tin-box/Creten-Speaker/V4_OuterShell_R.stl

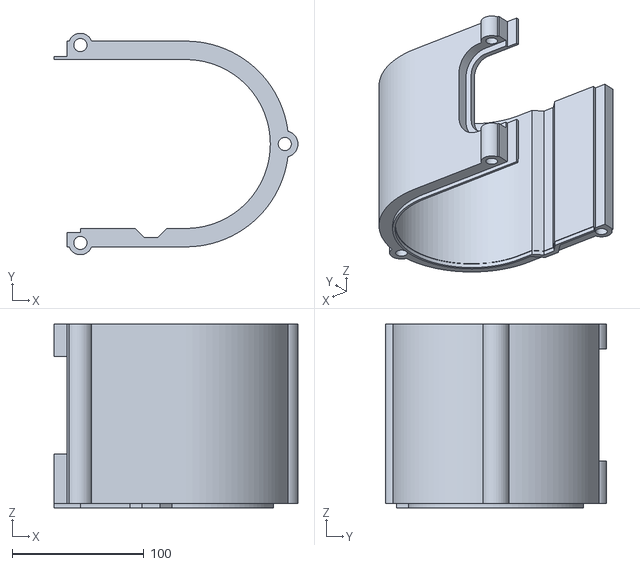
[picture p17: CAD file, 2023-01-02]
V4_OuterShell_R.stl
185.0 x 167.9 x 139.5
