tin-box/Creten-Speaker/V4_BottomPlate_L.stl

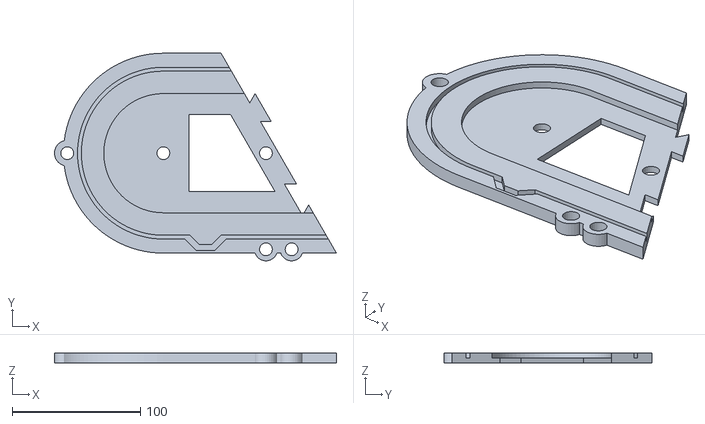
[picture p18: CAD file, 2023-01-02]
V4_BottomPlate_L.stl
220.0 x 162.0 x 8.00
