tin-box/Creten-Speaker/Long_Dual_Pin.stl

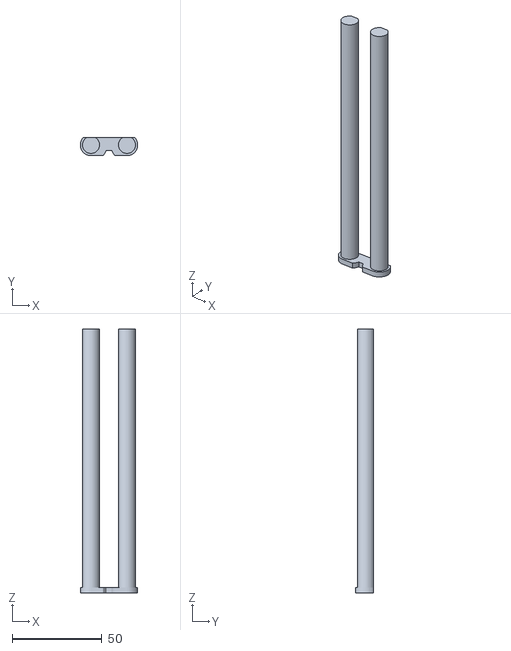
[picture p19: CAD file, 2023-01-02]
Long_Dual_Pin.stl
32.0 x 10.2 x 147.0
