tin-box/Creten-Speaker/QuadTopCap.stl

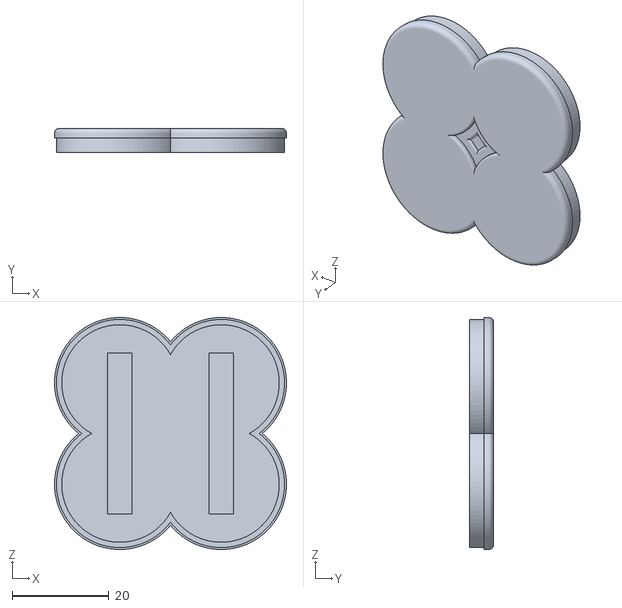
[picture p20: CAD file, 2023-01-02]
QuadTopCap.stl
48.0 x 5.00 x 48.0
