tin-box/Creten-Speaker/QuadControlPanelNoLamp.stl

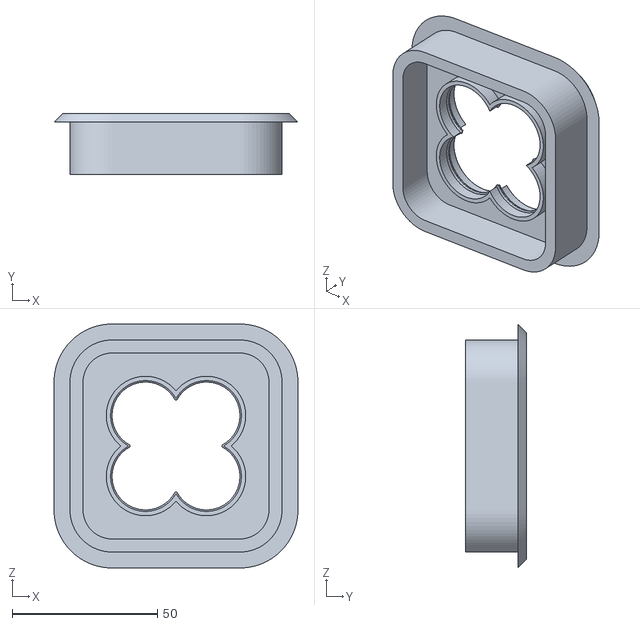
[picture p21: CAD file, 2023-01-02]
QuadControlPanelNoLamp.stl
84.0 x 21.0 x 84.0
