tin-box/Creten-Speaker/V4_PwrPlug.stl

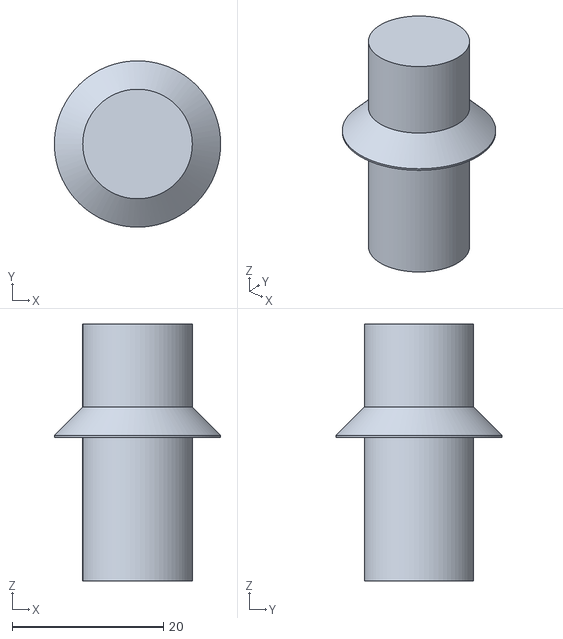
[picture p22: CAD file, 2023-01-02]
V4_PwrPlug.stl
22.0 x 22.0 x 34.0
