tin-box/Creten-Speaker/V4_VolKnob6mm.stl

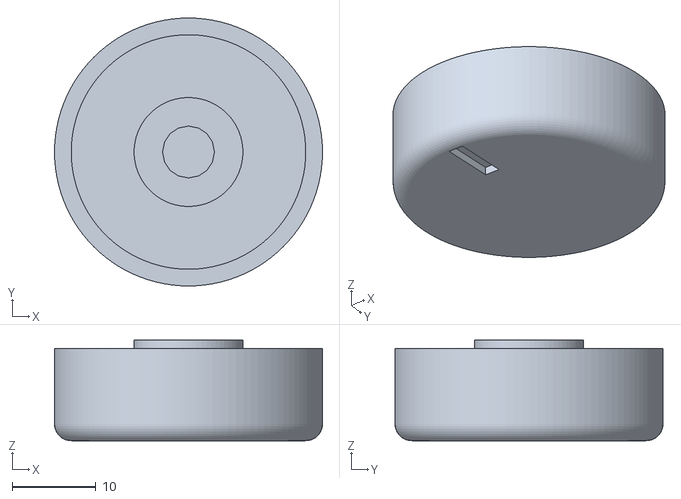
[picture p23: CAD file, 2023-01-02]
V4_VolKnob6mm.stl
32.0 x 32.0 x 12.0
