tin-box/Creten-Speaker/Quad18650Tube.stl

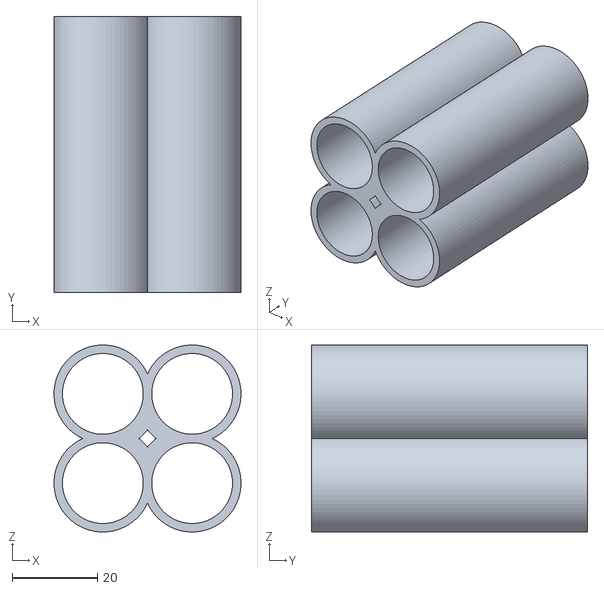
[picture p24: CAD file, 2023-01-02]
Quad18650Tube.stl
44.0 x 65.0 x 44.0
