tin-box/Creten-Speaker/V4Nut.stl

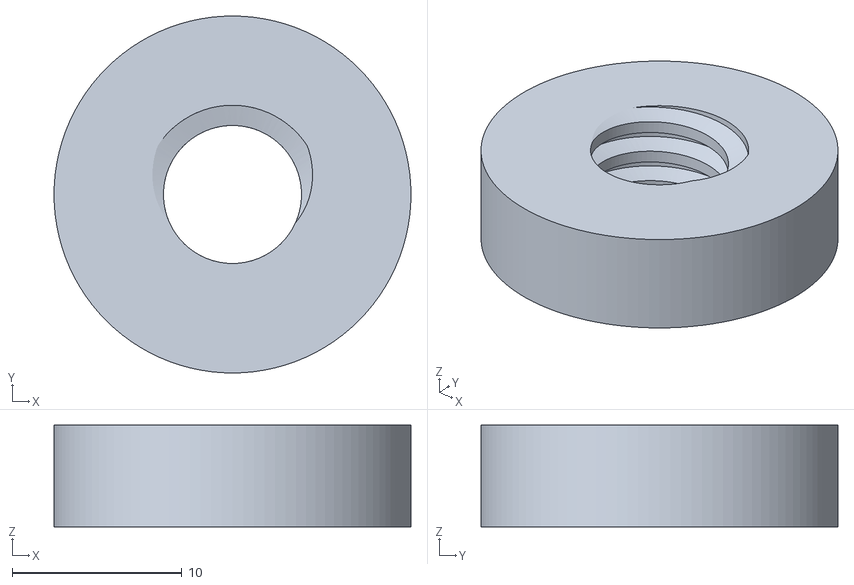
[picture p25: CAD file, 2023-01-02]
V4Nut.stl
21.0 x 21.0 x 6.00
