tin-box/Creten-Speaker/V4_QuadControlPanel_V3.stl

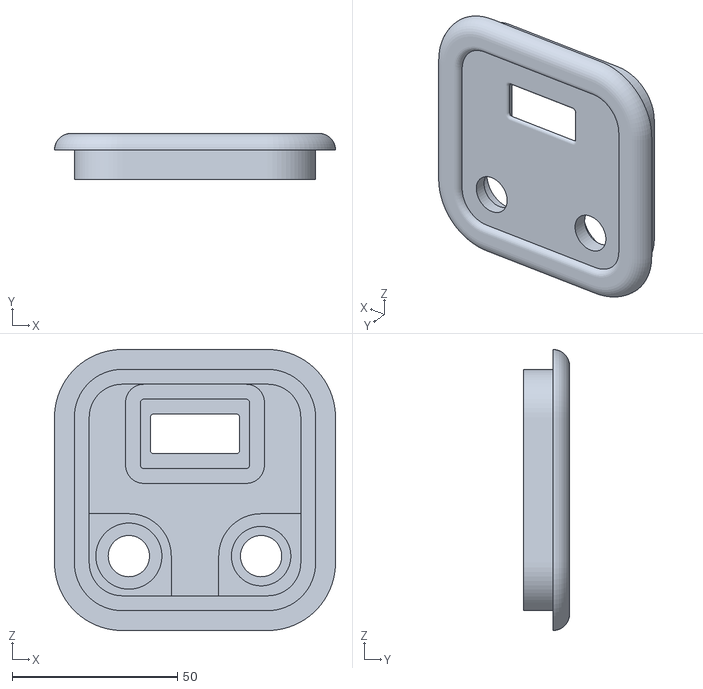
[picture p26: CAD file, 2023-01-02]
V4_QuadControlPanel_V3.stl
85.0 x 14.0 x 85.0
