tin-box/Creten-Speaker/V4_InnerHalfNoBottom_L.stl

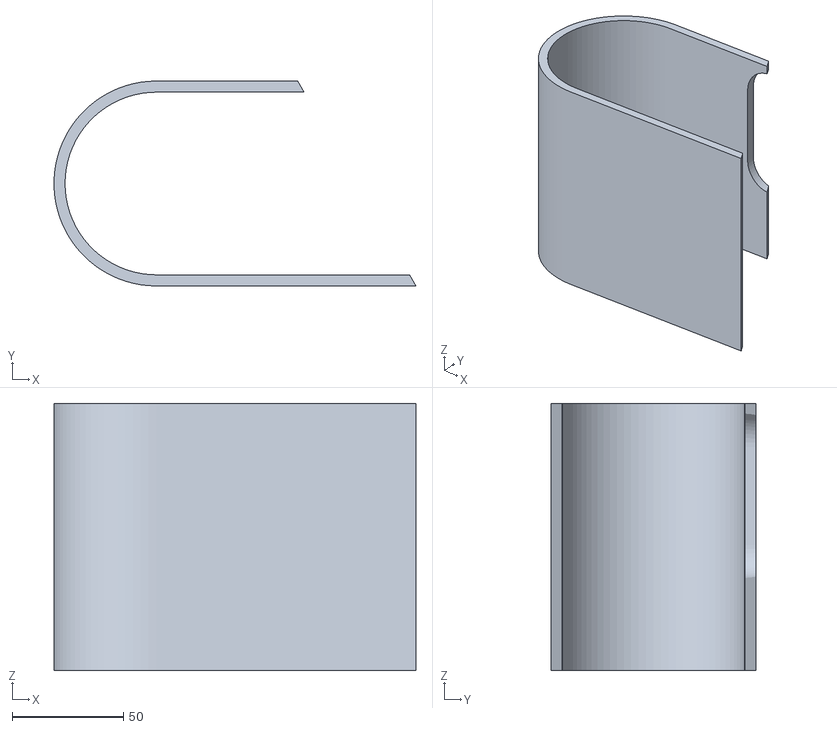
[picture p27: CAD file, 2023-01-02]
V4_InnerHalfNoBottom_L.stl
162.5 x 92.0 x 120.0
