tin-box/Creten-Speaker/V4_3InchMount.stl

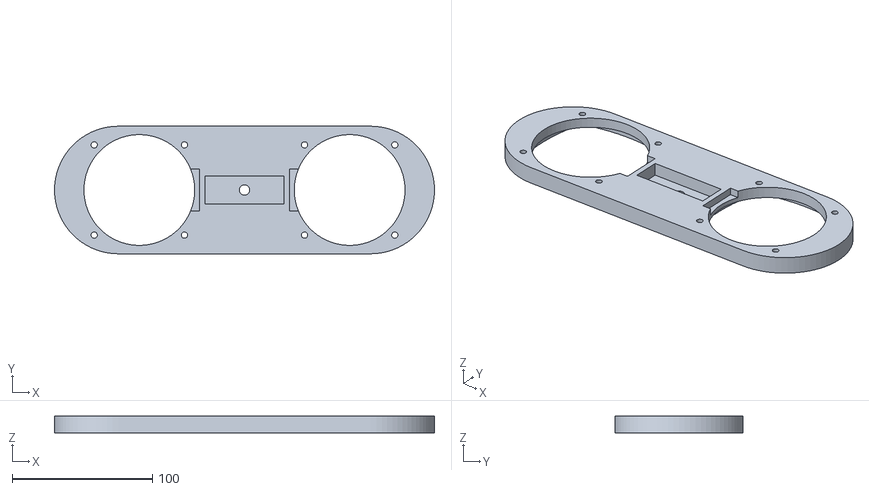
[picture p28: CAD file, 2023-01-02]
V4_3InchMount.stl
271.0 x 91.0 x 12.0
