tin-box/Creten-Speaker/QuadControlPanel.stl

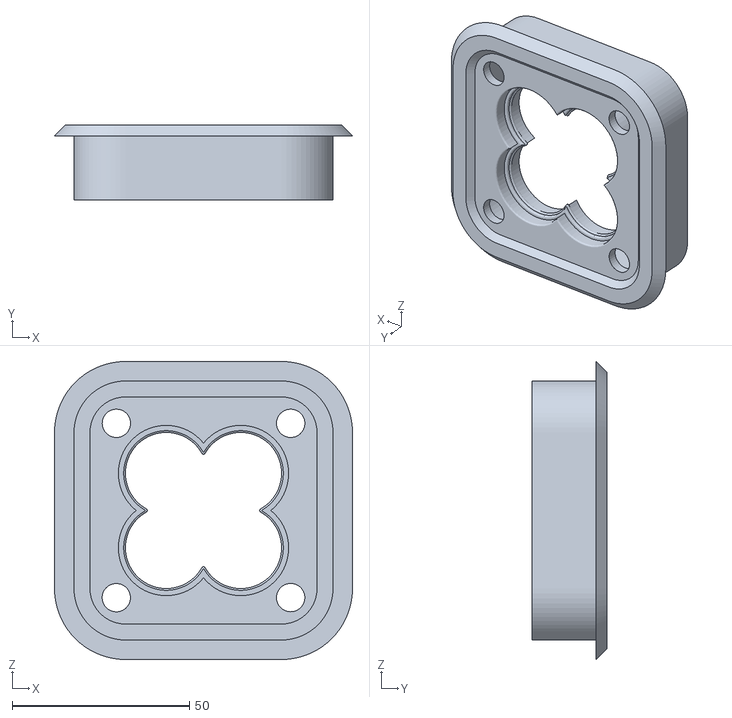
[picture p29: CAD file, 2023-01-02]
QuadControlPanel.stl
84.0 x 21.0 x 84.0
