tin-box/Creten-Speaker/QuadTopCap_Bridge.stl

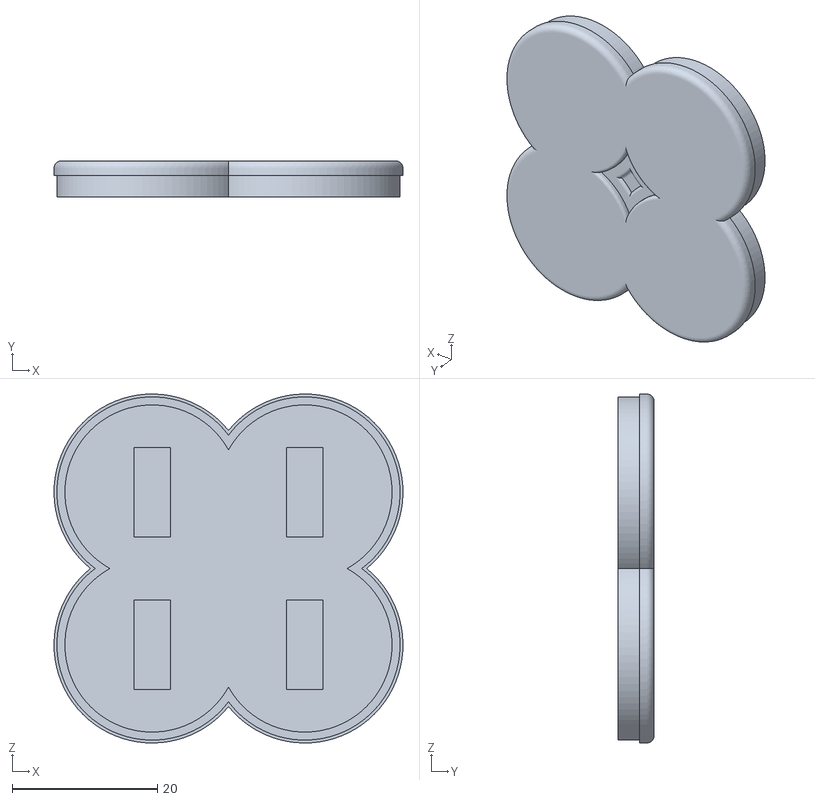
[picture p30: CAD file, 2023-01-02]
QuadTopCap_Bridge.stl
48.0 x 5.00 x 48.0
