tin-box/Creten-Speaker/V4_Liner.stl

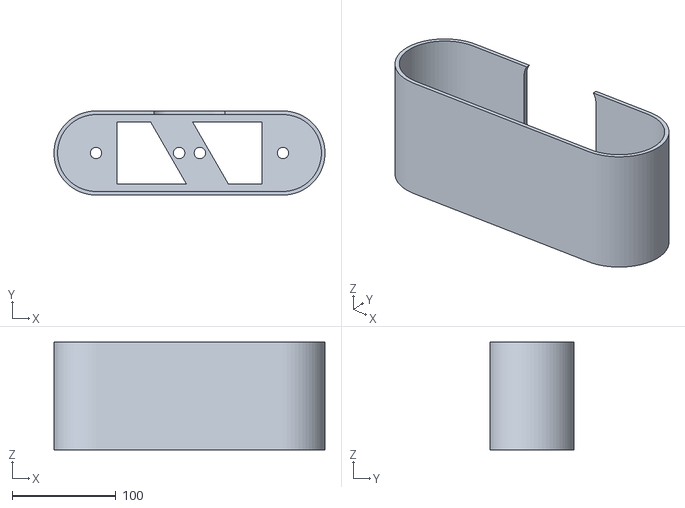
[picture p31: CAD file, 2023-01-02]
V4_Liner.stl
260.9 x 81.0 x 103.5
