tin-box/Creten-Speaker/USB_Plug3.8mmdiameter.stl

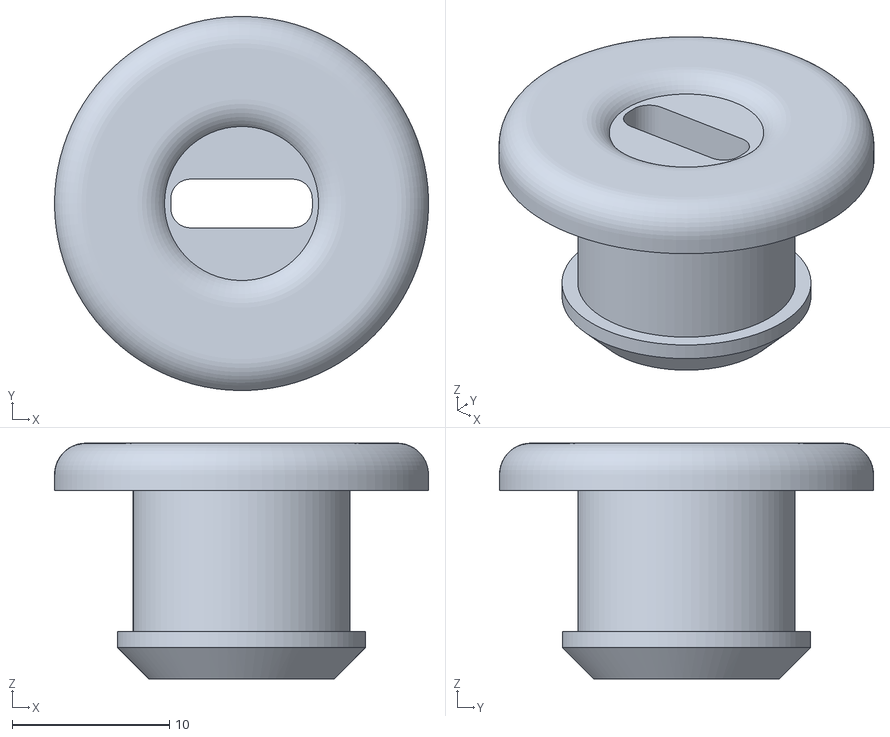
[picture p32: CAD file, 2023-01-02]
USB_Plug3.8mmdiameter.stl
23.8 x 23.8 x 15.0
