tin-box/Creten-Speaker/QuadBaseCap.stl

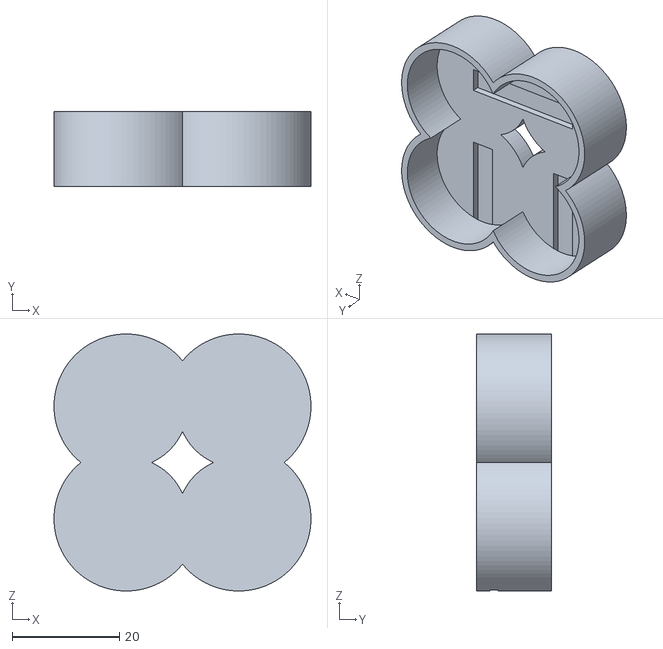
[picture p33: CAD file, 2023-01-02]
QuadBaseCap.stl
48.0 x 14.0 x 48.0
