tin-box/Creten-Speaker/V4_InnerHalf_R.stl

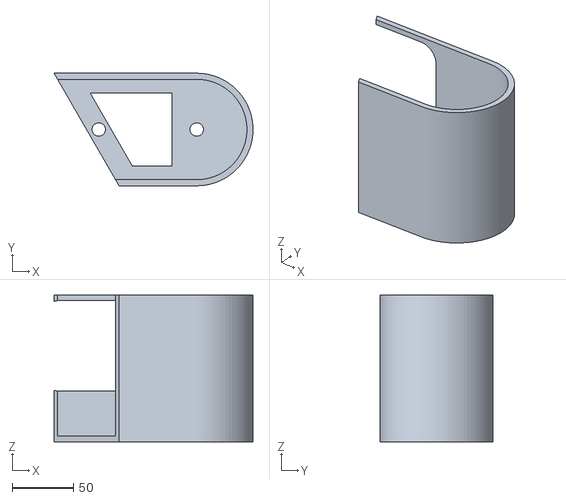
[picture p34: CAD file, 2023-01-02]
V4_InnerHalf_R.stl
162.5 x 92.0 x 120.0
