tin-box/Creten-Speaker/V4_WoodPattern.stl

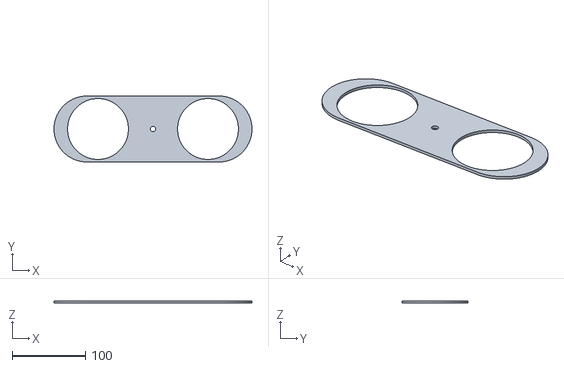
[picture p35: CAD file, 2023-01-02]
V4_WoodPattern.stl
270.0 x 90.0 x 3.00
