tin-box/Creten-Speaker/V4_InnerTopPwr.stl

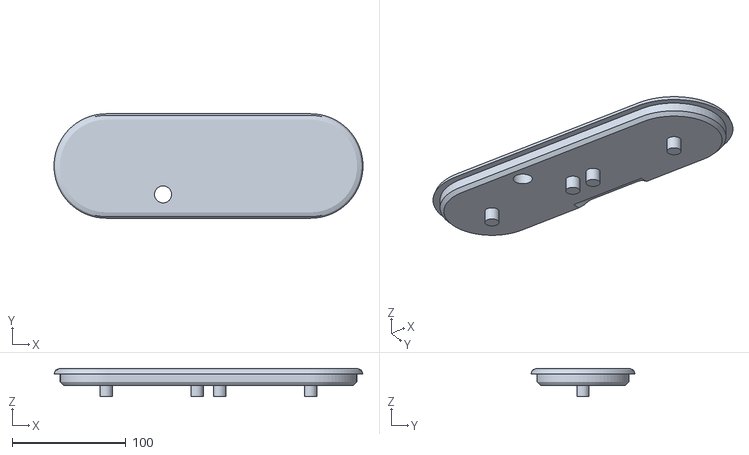
[picture p36: CAD file, 2023-01-02]
V4_InnerTopPwr.stl
272.0 x 92.0 x 25.0
